emeb/ice-dongle/Gateware/riscv_lcd/c/i2c.h

/*
 * i2c.h - I2C IP core driver
 * 06-23-20 E. Brombaugh
 */

#ifndef __i2c__
#define __i2c__

#include "riscv_lcd.h"

/* i2c functions */
void i2c_init(I2C_TypeDef *s);
int8_t i2c_mtx(I2C_TypeDef *s, uint8_t addr, uint8_t *data, uint8_t sz);
int8_t i2c_srx(I2C_TypeDef *s, uint8_t addr, uint8_t *data, uint8_t sz);

#endif
